YeetTheAnson/MerlynCAM/cartScreenshots/AliExpressCheckout.png

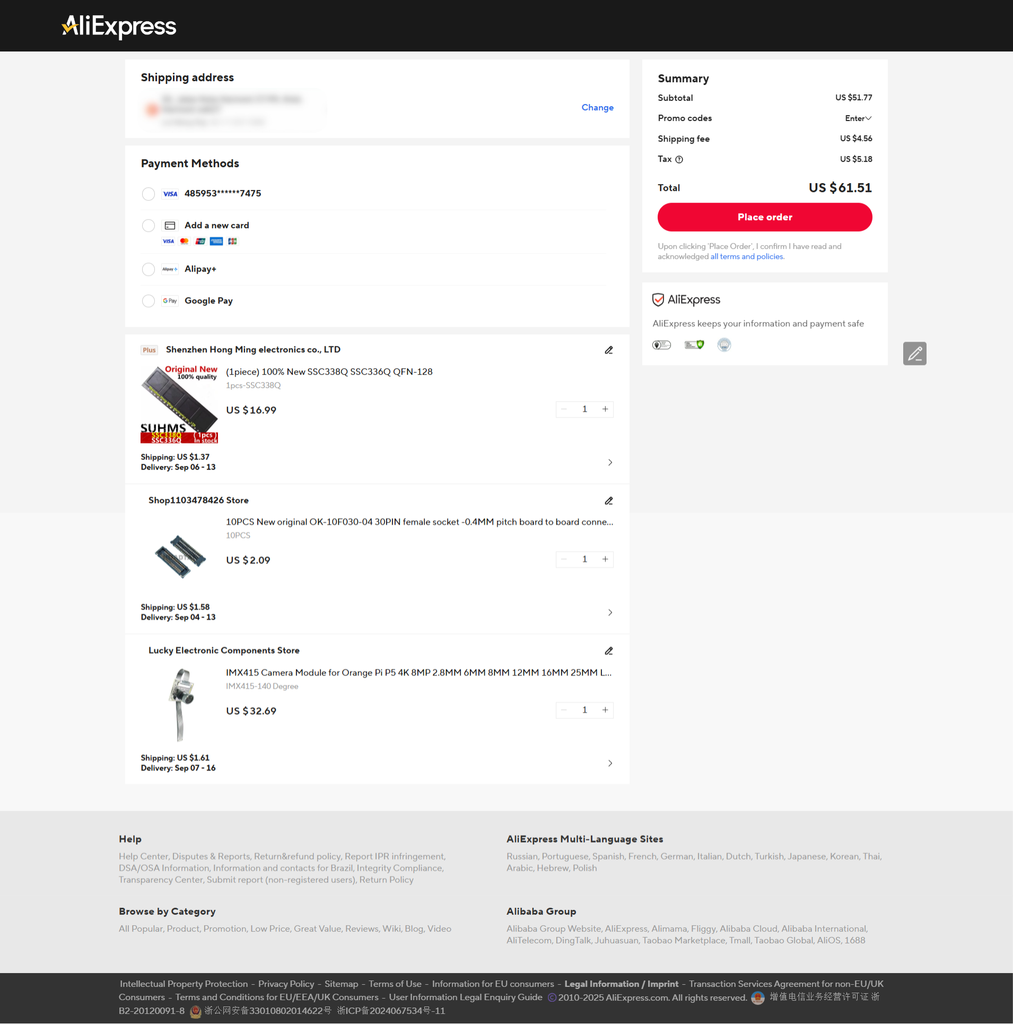
cartScreenshots/AliExpressCheckout.png
