YeetTheAnson/MerlynCAM/cartScreenshots/JLCCart.png

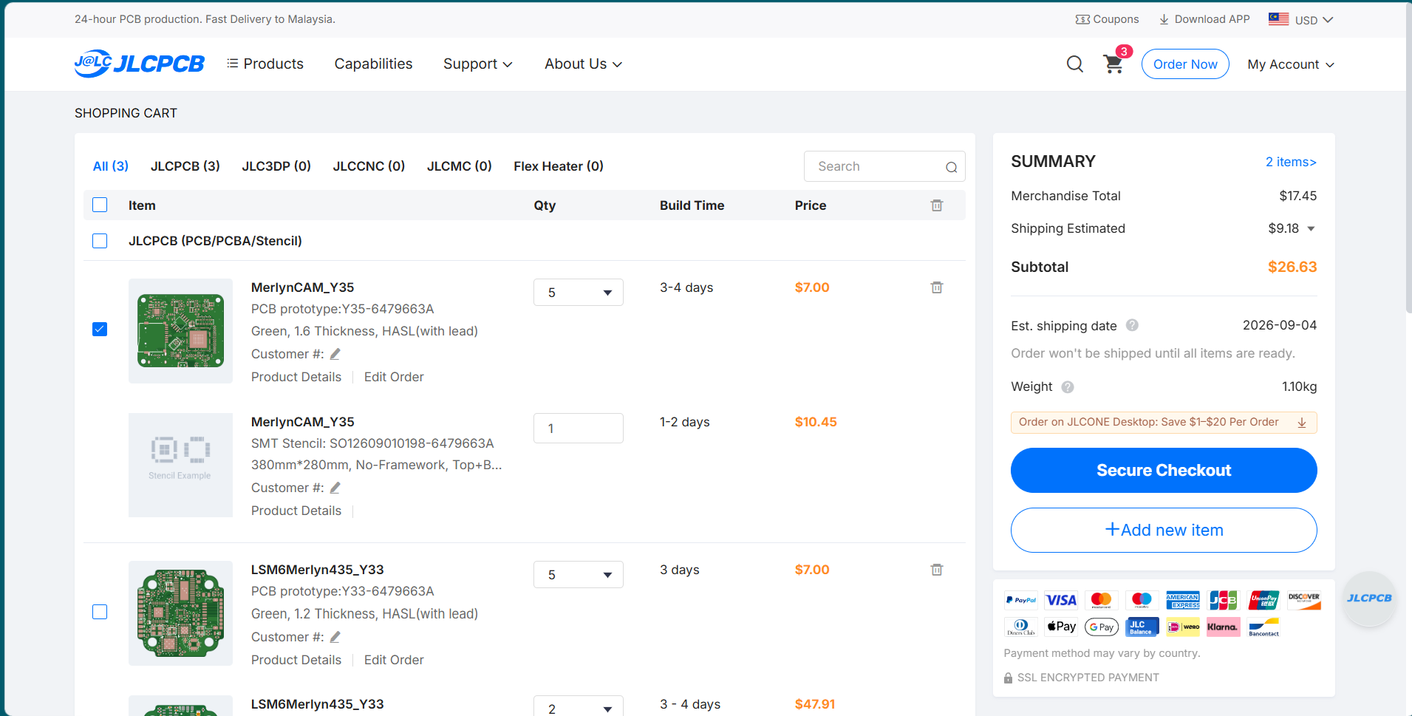
cartScreenshots/JLCCart.png
