YeetTheAnson/MerlynCAM/cartScreenshots/JLCShipping.png

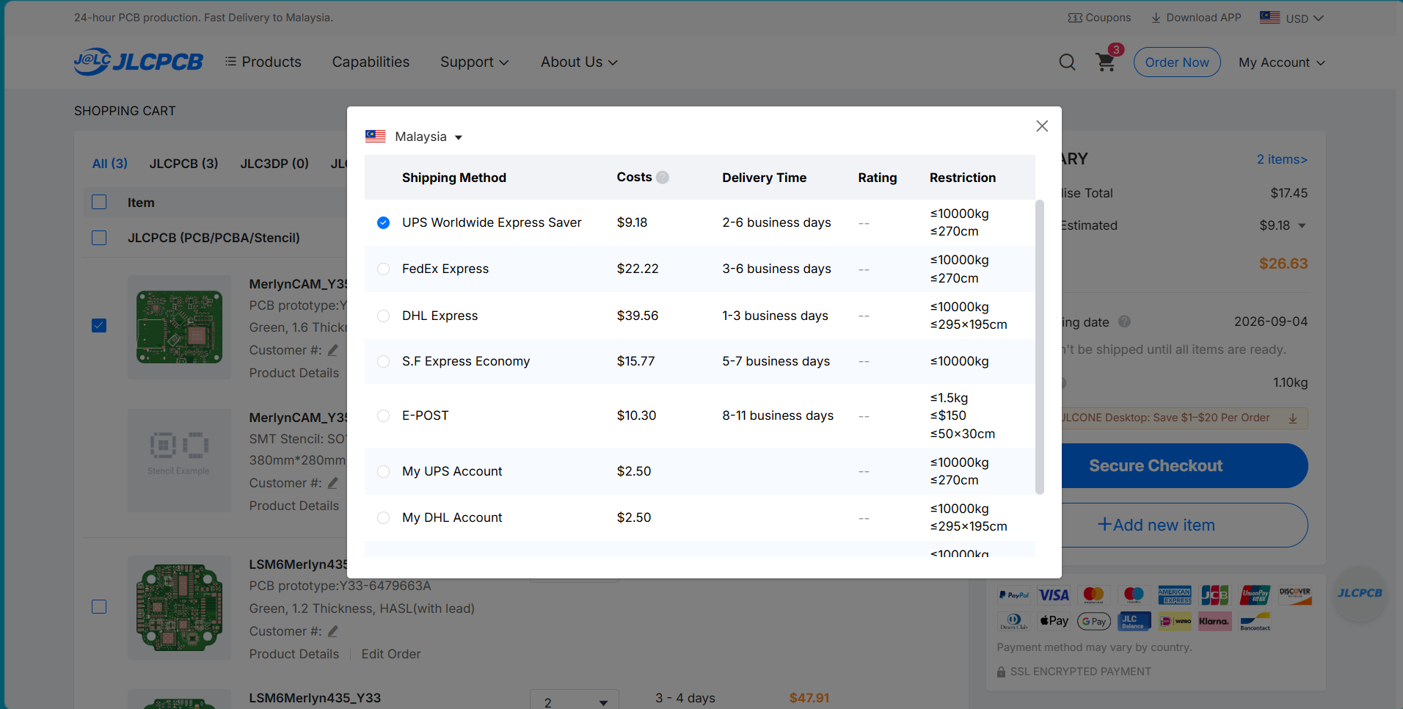
cartScreenshots/JLCShipping.png
